Elecrow-RD/CrowPanel-Pico-Display-2.4-inch-320240/factory_firmware/3.jpg

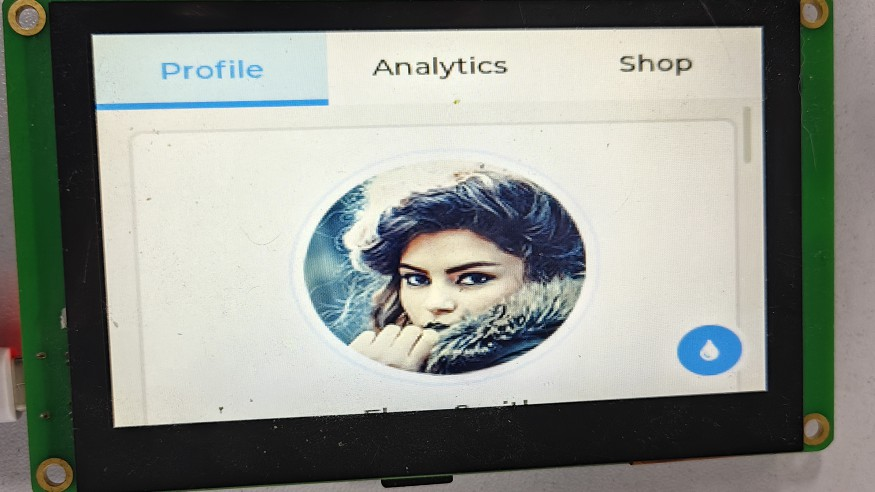
factory_firmware/3.jpg
