Elecrow-RD/CrowPanel-Pico-Display-2.4-inch-320240/example/Arduino/UI_Code&Material/UI Material/background.png

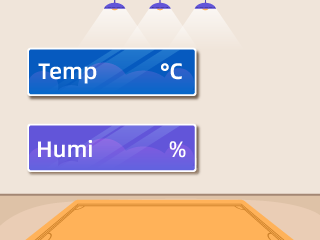
example/Arduino/UI_Code&Material/UI Material/background.png
