Elecrow-RD/CrowPanel-Pico-Display-2.4-inch-320240/example/Arduino/2.4_Libraries/XPT2046_Touchscreen/doc/ILI9431Test.jpg

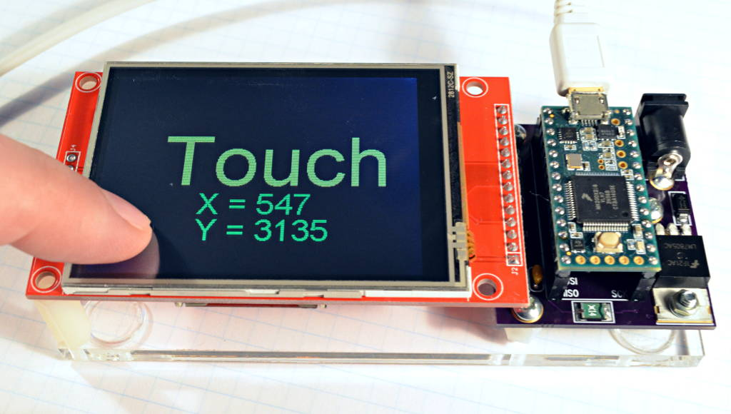
example/Arduino/2.4_Libraries/XPT2046_Touchscreen/doc/ILI9431Test.jpg
